Ja-Jager/griddles/docs/炸炉会议记录.md

# 会议记录

## 230109

时间：下午三点

参与方：陈希、丁鹏、杜淇宇

### 讨论内容

1. 早上大家的工作进度
    1. 阿杜：MAX6675 队列
    2. 阿鹏：主函数，队列邮箱，`protect`、seg、relay 已完成
    
2. Toaster 烘包机 driver 进度
    1. 完成：
       1. `protect`、seg、relay 之间
    2. 没完成：
       1. nvs 不需要用任务
       2. 按键
       3. 跨任务通信最花时间
          1. 

| **任务** | **负责人** | **完成了吗？** | 完成时间 |
| --- | --- | --- | --- |
| HC-SR04 | 阿鹏 | ✔ |  |
| MAX6675 | 阿杜 | ❌ |  |
| Nvs | 阿鹏 | ✔ |  |
| Protect | 阿杜 | ✔ |  |
| Relay | 阿鹏 | ✔ |  |
| SegmentDisplay | 阿鹏 | ✔ |  |
| Switch | 阿鹏 | ✔ |  |
| vl53l0x | 阿鹏 | ✔ |  |
| 主函数 | 阿鹏&阿杜  | ❌ |  |

2. ESP-IDF v5.0 升级 toaster
   1. 鹏没有问题
   2. 阿杜需要编译烘包机测试

3. 基于新增功能修改现有逻辑流程图
4. 炸炉引脚分配，如何减少引脚
   1. 用片选 IC

5. 炸炉增加 PWM 控温
6. 把 driver 里的代码移动到 component 中
7. 接下来的工作安排
   1. 阿杜：旋转编码器
   2. 阿鹏：继续主函数
      1. 炸炉：陈希提供阿鹏倒计时有什么函数
