Ja-Jager/griddles/docs/希与ROBIN的会议.md

# 希与ROBIN的会议

会议时间：2023.7.13

参会人员：希、ROBIN

会议目的：研究M3000（frymaster）的现有功能信息

希所能了解到的M3000的信息：

1. 油温（输入）

2. 蜂鸣器（输出）

3. 继电器（输出）

4. 升降机（输出）（暂未查出）

ROBIN的看法：

1. ROBIN认为蜂鸣器只能做到响来反映炸过一次菜单，但具体不知道是哪个菜单，什么时间点操作菜单。

2. 对于能耗，用电，现在只知道用的是哪个槽哪个继电器的吸合、断开，PWM，只能知道能耗是大是小，但还需知道它频率多少，用了多少电。假如发热管功率有衰减，只看继电器，能耗是看不出来的。需要有方法知道继电器的实时功率、功耗。

3. * 人生安全、财产安全：短路、着火，这些需要有故障提示
   
   * 食品安全：性能衰减，导致食物品质不行，性能方面的情况也需有故障提示
   
   需要当遇到故障时，需读取到一些故障代码，运行讯息。

4. 有没有可能远程修改菜单

5. ROBIN认为现在板子发出什么就把那个信号抓取，他发出的是哪一路的逻辑什么条件下触发 ，会出现什么报警，需破解其代码，破解它的控制。

6. 从烹饪的角度，要知道什么温度开启加热，什么温度停止加热，什么安全条件会出现报警，没达到什么条件会什么报警，是怎么进行温度补偿。

7. 这些输出量得研究，分难易先后去查找。

总结：

1. 暂时得到的这些油温、蜂鸣器、继电器、升降机不足以获取到炸炉的一些更细致的信息

2. 需了解电子板工作时，用了什么菜单、什么时候用的

3. 需了解电子板通过什么方式了解到发热管的实时功率、能耗

4. 需了解电子板在安全、品质方面是否有些故障提示

5. 需了解电子板是否有远程操作菜单、修改菜单的功能

6. ROBIN的建议：
   
   1. 需将板子上的输出量读取，发出接受什么信号就读什么信号
   
   2. 需破解其代码，了解其控制
   
   3. 对于以上这些，分难易先后去查找
