Ja-Jager/griddles/docs/技术文档(内部)/K型热电偶与热敏电阻的对比.md

# 热电偶与热敏电阻的测试对比

---

## 四探头

| 四探头绝缘 | 四探头位置 | 四探头的外部热传导 |四个探头的具体外观|
| --- | --- | --- |---|
|  |  |  ||

如图以上四图为了四个测温设备的互不干扰与公平，绝缘胶的层数相同，并用锡箔纸覆盖。

## 测试数据

### 测试操作

将温度处于室温的四个探头放入分3次投放入不同温度的液体中，观察其变化并记录，并记录在温度采集最稳定阶段的温度

### 温度数值

|测温设备| 80℃（沸水） | 114℃（油） | 168℃（油） |
|---| --- | ---- | ---- |
|**手持式温度计A**| 79.8℃ | 114.4℃ | 168℃ |
|**手持式温度计B**| 80.1℃ | 112.3℃ | 168℃ |
|**热敏电阻**| 80.54℃ | 111.84℃ | 158℃ |
|**热电偶**| 80.25℃ | 115℃ | 164℃ |

### 数据依据

| 80℃（沸水） | 114℃（油） | 160℃（油） |
| --- | --- | --- |
|  |  |  |

### 具体表格

| 80℃ |  |
| --- | --- |
| **114℃** |  |
| **168℃** |  |

## 结论

通过观察，热电偶的反应速度要快于热敏电阻的反应速度，且当温度平稳时，相较于热敏电阻，测出的温度更接近手持温度计的。故而热电偶优于热敏电阻。
