Ja-Jager/griddles/docs/技术文档(内部)/高端炸爐操作指南.md

# 高端炸爐操作指南

***更新时间：2023/9/11 18：00***

[TOC]

## 語言切換

1. 用戶通過左邊的橫欄【手动】、【计时】、【设置】，按下【设置】以**選擇**設置。

2. 滑動如下圖的**語言切換滾輪**。



### 使用流程

用戶通過自己的需求，可以用撥動**語言切換滾輪**來選擇心儀的語言。只要修改了，所有頁面的大多語言都會被修改。

## 手動操作

alt jpg

alt jpg

手動操作可以操作的位置有如上圖的4個位置。

1. 設定溫度滑條（量程：100℃ ~ 200℃，200℉ ~ 400℉）

2. 設定倒計時滑條（量程：15min，滑動的最小一格為10s）

3. 開始鍵

4. 旋鈕及旋鈕按鍵

### 烹飪流程

#### 用戶自定義操作

1. 用戶通過左邊的橫欄【手动】、【计时】、【设置】，按下【手动】以選擇**手動模式**。

2. 用戶通過自己的需求，可以用滑條或旋鈕**調整設定溫度**。（建議：滑條用於大幅度調整，旋鈕用於微小調整）。

3. 用戶通過自己的需求，可以用滑條**調整設定倒計時**。

4. 按下開始鍵或旋鈕，機器就會**開啓加熱**。

5. 按下開始鍵后，當溫度還**未到達設定溫度**時，【倒計時】下會顯示【預熱中】。

6. 當溫度達到設定溫度時，會出現一個頁面，提示投放食物。投放完食物后，按下屏幕上的【DONE】，**倒計時開啓**。

7. 當倒計時結束或客戶再次按下開始鍵或旋鈕按鍵，機器就會**結束倒計時，停止加熱**。

#### 无倒计时操作

1. 用戶通過自己的需求，可以用滑條或旋鈕調整設定溫度。（建議：滑條用於大幅度調整，旋鈕用於微小調整）。

2. 當溫度滑條拉至最左端，此時【設定倒計時】下會顯示【持續運行】。

3. 按下開始鍵或旋鈕，機器就會**開啓加熱**。

4. 按下開始鍵后，當溫度還**未到達設定溫度**時，【倒計時】下會顯示【預熱中】。

5. 當溫度**達到設定溫度**時，會出現一個頁面，提示投放食物。投放完食物后，按下屏幕上的【DONE】。

6. 客戶再次按下開始鍵，機器就會**停止加熱**。

## 自動操作

alt jpg



自動操作可以操作的位置有如上圖的3個位置。

1. 菜單滾輪

2. 開始鍵

3. 旋鈕及旋鈕按鍵

### 烹飪流程

1. 用戶通過左邊的橫欄【手动】、【计时】、【设置】，按下【自动】以選擇**自動模式**。

2.  用戶通過自己的需求，可以用滾輪或旋鈕**選擇**自己想要的**菜單**。

3. 按下開始鍵或旋鈕，機器就會**開啓加熱**。

4. 按下開始鍵后，當溫度還**未到達設定溫度**時，【倒計時】下會顯示【預熱中】。

5. 當溫度**達到設定溫度時**，會出現一個頁面，提示**投放食物**。投放完食物后，按下屏幕上的【DONE】，**倒計時開啓**。

6. 客戶再次按下開始鍵，機器就會**停止加熱**。

7. 當用戶用自動模式開啓加熱時，如果沒有切換界面，按下任何物理按鍵、開始鍵和滑動滾輪，就會彈出一個**屏保頁面**，類似與下圖。顯示的内容：倒計時、菜單名。

alt jpg

## 菜單操作

1. 用戶通過左邊的橫欄【手动】、【计时】、【设置】，按下【设置】以**選擇**設置。

2. 點擊如下圖的【menu】。



3. 點擊過後進入**用戶菜單**就會出現如下圖的針對菜單的3個操作：新增菜單、修改菜單、刪除菜單。



### 新增菜單

點擊**用戶菜單**的【Create Menu】,進入如下圖的**新增菜單頁面**。



新增菜單可以操作的位置有如上圖的4個位置。

1. 設定溫度滑條（量程：100℃ ~ 200℃，200℉ ~ 400℉）

2. 設定倒計時滑條（量程：15min，滑動的最小一格為10s）

3. 菜單列表

4. 新增菜單鍵

#### 使用流程

1. 用戶通過自己的需求，可以用滑條**調整設定溫度**。

2. 用戶通過自己的需求，可以用滑條**調整設定倒計時**。

3. 用戶通過自己的需求，可以用下拉式列表**選擇**心儀的**菜單名**。

4. 用戶確定完自己的選擇後，通過按下新增菜單鍵來**新增菜單**，新增的菜單出現將在**自動操作的滾輪選項**中。

### 編輯菜單

點擊**用戶菜單**的【Edit Menu】,進入如下圖的**編輯菜單頁面1**。

alt jpg

可以操作的位置有如上圖的2個位置。

1. 菜單列表（此列表中的選項都是自動操作頁面的滾輪選項）

2. 菜單名確定鍵

點擊**編輯菜單頁面1**的菜單確定鍵，進入如下圖的**編輯菜單**頁面2。

alt jpg

可以操作的位置有如上圖的3個位置。

1. 設定溫度滑條（量程：100℃ ~ 200℃，200℉ ~ 400℉）

2. 設定倒計時滑條（量程：15min，滑動的最小一格為10s）

3. 菜單修改確定鍵

#### 使用流程

1. 用戶通過自己的需求，可以用**菜單列表**選擇需要修改的**自動操作頁面的菜單選項**。

2. 按下菜單名確定鍵，進入**編輯菜單頁面2**。

3. 進入**編輯菜單頁面2**后，用戶通過自己的需求，可以用滑條**修改設定溫度**。

4. 用戶通過自己的需求，可以用滑條**修改設定倒計時**。

5. 用戶確定完自己的要修改的選擇後，通過按下**菜單修改確定鍵**來**修改菜單**，修改后的菜單會更新到**自動操作的滾輪選項**中。

### 刪除菜單

點擊**用戶菜單**的【Delete Menu】,進入如下圖的**刪除菜單頁面**。

alt jpg

可以操作的位置有如上圖的2個位置。

1. 菜單名滾輪（此列表中的選項都是自動操作頁面的滾輪選項）

2. 菜單刪除確定鍵

#### 使用流程

1. 用戶通過自己的需求，可以用**菜單名滾輪**選擇需要刪除的**自動操作頁面的菜單選項**。

2. 用戶確定完自己的要刪除的選擇後，通過按下**菜單刪除確定鍵**來**刪除菜單**，刪除后，菜單會更新到**自動操作的滾輪選項**中。

## 溫度單位切換

1. 用戶通過左邊的橫欄【手动】、【计时】、【设置】，按下【设置】以**選擇**設置。

2. 點擊如下圖的**溫度單位切換開關**。

alt jpg

### 使用流程

用戶通過自己的需求，可以用撥動**溫度單位切換開關**來選擇心儀的單位。只要修改了，手動操作、自動操作、新增菜單、修改菜單中的設定溫度和當前溫度的單位都會隨之變化。

## 演示模式

1. 用戶通過左邊的橫欄【手动】、【计时】、【设置】，按下【设置】以**選擇**設置。

2. 點擊如下圖的**演示模式開關**。



### 使用流程

當用戶對電子板不施加强電以供電時，可將**演示模式開關**打開，這樣就可以不受超溫保護、發熱管、泄油閥的影響用於演示。

**注意：當正常使用時，一定要關閉演示模式，否則超溫保護、發熱管、泄油閥將會失效。**

## 物理按鍵切換操作頁面



用戶可通過上圖的【模式】物理按鍵來切換操作頁面。

* 如果當前處於**自動操作頁面**，按下該鍵就會切換至**手動操作頁面**。

* 如果當前處於**手動操作頁面**，按下該鍵就會切換至**自動操作頁面**。

## 超溫保護、泄油、發熱管擡起

只要有出現**超溫保護、泄油、擡起發熱管**，機器將立刻**停止加熱，停止倒計時**。

**注意：正常烹炸食物時，一定要將演示模式關閉。**
