Ja-Jager/griddles/docs/技术文档(内部)/AVR版本/原高端炸炉引脚分配.md

# 原高端炸炉引脚分配

***更新于2023.2.1 10:30***

| 引脚名称 | 作用 |
| --- | --- |
| PE6/AOT2（LSW_A3） | 低电平使继电器通电，使得**左端子**的12、15脚相连，实现相关功能，信息反馈给LIN_B3引脚 |
| PE5/AOT3（LSW_A2） | 低电平使继电器通电，使得**左端子**的5、13脚相连，实现相关功能，信息反馈给LIN_B5引脚 |
|PE4/AOT4（LSW_A1）|低电平使继电器通电，使得**左端子**的10、12脚相连，实现相关功能，信息反馈给LIN_B3引脚|
|PE3/AOT5（ASW_1）|低电平使继电器通电，使得ACOUTA与交流220V相连，此功能现在空置，ACOUTA功能未知|
|PE2/AOT6（ASW_2）|低电平使继电器通电，使得ACOUTB与交流220V相连，此功能现在空置，ACOUTB功能未知|
|PG5/AOT8|使能蜂鸣器|
|PH0/LIN_B1|**左端子**的2、7脚相连，信息反馈给LIN_B1|
|PH1/LIN_B2|**左端子**的6、11脚相连，信息反馈给LIN_B2|
|PH2/LIN_B3|参考上述AOT2、4|
|PH3/LIN_B4|**左端子**的4、8脚相连，信息反馈给LIN_B4|
|PH4/LIN_B5|参考上述AOT3|
|PJ6/LROUT5(RSW_A3)|低电平使继电器通电，使得**右端子**的12、15脚相连，实现相关功能，信息反馈给RIN_B3引脚|
|PJ5/LROUT6(RSW_A2)|低电平使继电器通电，使得**右端子**的5、13脚相连，实现相关功能，信息反馈给RIN_B5引脚|
|PJ4/LROUT7(RSW_A1)|低电平使继电器通电，使得**右端子**的10、12脚相连，实现相关功能，信息反馈给RIN_B3引脚|
|PJ3/LROUT8(DATA_OUT)|备用接口，连接JP1，此功能空置|
|PC6/DATA_INA|备用接口，连接JP1，JP1将信息反馈给DATA_INA，此功能空置|
|PC5/DATA_INB|备用接口，连接JP1，JP1将信息反馈给DATA_INB，此功能空置|
|PC4/RIN_B1|**右端子**的2、7脚相连，信息反馈给RIN_B1|
|PC3/RIN_B2|**右端子**的6、11脚相连，信息反馈给RIN_B2|
|PC2/RIN_B3|参考上述LROUT5、7|
|PC1/RIN_B4|**右端子**的4、8脚相连，信息反馈给RIN_B2|
|PC0/RIN_B5|参考上述LROUT6|
|PL3/X_SW_1|连接显示按键接口|
|PL2/X_SW_2|连接显示按键接口|
|PL1/X_SW_3|连接显示按键接口|
|PL0/X_SW_4|连接显示按键接口|
|PD6/X_DIO|连接显示按键接口|
|PD5/X_CLK|连接显示按键接口|
|PD4/X_ASTB|连接显示按键接口|
|PD1/X_BSTB|连接显示按键接口|
|PD0/X_CSTB|连接显示按键接口|
|PL7/X_DSTB|连接显示按键接口|
|PL6/X_ESTB|连接显示按键接口|
|PL5/X_FSTB|连接显示按键接口|
|PL4/X_GSTB|连接显示按键接口|
|PA3/IN1A|备用接口，连接U13，此功能空置|
|PA4/IN1B|备用接口，连接U13，此功能空置|
|PA5/IN2A|备用接口，连接U12，此功能空置|
|PA6/IN2B|备用接口，连接U12，此功能空置|
|PJ2/485_EN|备用接口，RS485通讯，此功能空置|
|PJ0/485_RXD|备用接口，RS485通讯，此功能空置|
|PJ1/485_TXD|备用接口，RS485通讯，此功能空置|
|PG1/EP_DIO|用于EEPROM|
|PG0/EP_CLK|用于EEPROM|
|PD7/EP_STB|用于EEPROM|
|PH5/R_CLK|用于断电后提供时钟，可能用于显示实时时间|
|PH6/R_DIO|用于断电后提供时钟，可能用于显示实时时间|
|PB0/R_STB|用于断电后提供时钟，可能用于显示实时时间|
|PB1/SPI_SCK|用于烧写程序|
|PB2/SPI_MOSI|用于烧写程序|
|PB3/SPI_MISO|用于烧写程序|
|RESET/RESET|用于烧写程序时的复位，也可用于微处理器的复位|
|PK6/L_TER|用于左温度探头|
|PK7/R_TER|用于右温度探头|
|PK5/ADC_NTC|用于接收探头的反馈信息|
|PE0/RXD0|用于备用收发，此功能空置|
|PE1/TXD0|用于备用收发，此功能空置|
|PD2/RXD1|用于蓝牙、wifi功能收发|
|PD3/TXD1|用于蓝牙、wifi功能收发|
|AREF/AREF|基准电压输入引脚|

总共60个引脚，空置14个，实用46个。
