Ja-Jager/griddles/docs/技术文档(内部)/V2.2.0/关于稳压器件AMS1117过热的处理.md

# 关于稳压器件AMS1117过热的处理

***2023/7/3 16:00***

$$
P_{\text{Dissipated}} = (V_{\text{in}} - V_{\text{out}}) \times I
$$

$$
T_{\text{AboveAmbient}} = P_{\text{Dissipated}} \times 55
$$

$$
T_{\text{Final}} = T_{\text{Dissipated}} + T_{\text{Ambient}}
$$

$$
P_{\text{Dissipated}} = (5.00 - 3.281) \times I = 1.719I
$$

$$
T_{\text{AboveAmbientLOW}} = 1.719I\times 55=94.545I
$$

$$
T_{\text{AboveAmbientHI}} = 1.719I\times 80=137.52I
$$

$$
T_{\text{Final}} = T_{\text{DissipatedHI}} + T_{\text{Ambient}}
$$

$$
80=137.52I(LOW)+28
$$

$$
I(LOW)=0.378A
$$

$$
80=94.545I(HI)+28
$$

$$
I(HI)=0.550A
$$

[Microsoft Word - DS1117 (advanced-monolithic.com)](http://www.advanced-monolithic.com/pdf/ds1117.pdf)

参考第三页。

最终决定：将AMS1117封装从SOT-223换成TO-252，胶不覆盖器件表面，引脚可覆盖。
