Ja-Jager/griddles/docs/技术文档(内部)/V2.0.0/除了7寸屏外剩余的9个引脚分配.md

# 除了7寸屏外剩余的9个引脚分配

## 单独

| 功能 | 引脚占用数 |
| --- | --- |
| *** 温度探头（ADC）*** | 1 |
| ***继电器K9（ADC）*** | 1 |
|***4个按键（ADC）***|1|
| ***旋钮A*** | 1 |
| ***旋钮B*** | 1 |

## 多输出移位寄存器（74HC595）

| 功能 | 引脚总占用数 |
| --- | --- |
| 蜂鸣器 | 3 |

## 多输入移位寄存器（74HC165）

| 功能 | 引脚总占用数 |
| --- | --- |
| ***光耦P5*** | 2 |
| ***光耦P6*** | |
|***光耦P7***||
