Ja-Jager/griddles/docs/技术文档(内部)/流程图/微信图片_20230209092502.jpg

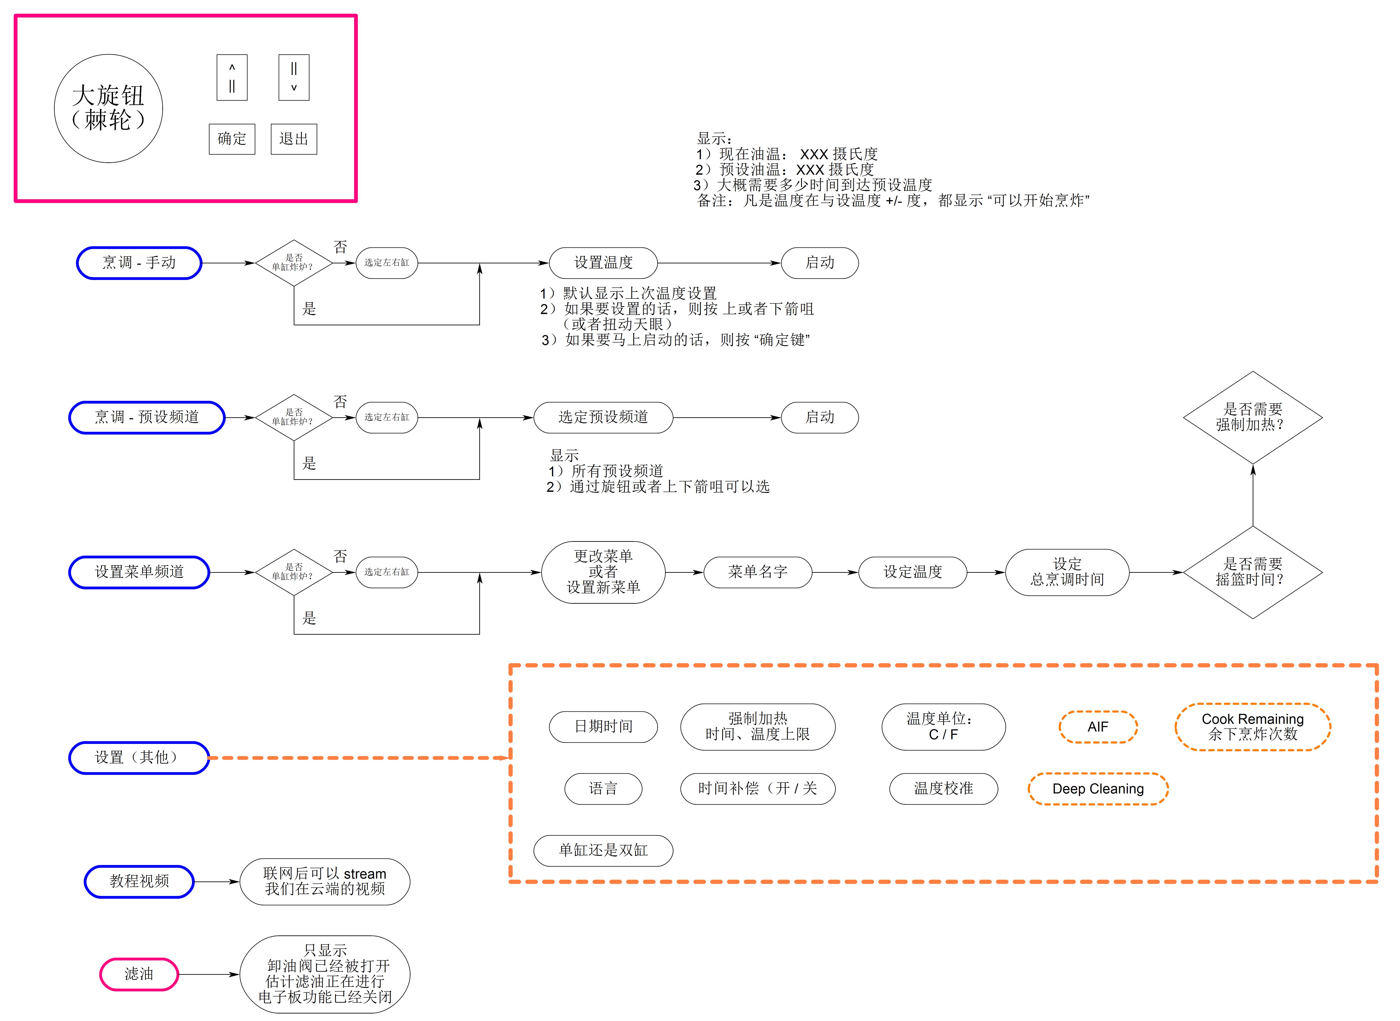
docs/技术文档(内部)/流程图/微信图片_20230209092502.jpg
