Ja-Jager/griddles/docs/技术文档(内部)/流程图/自定义菜单流程图.jpg

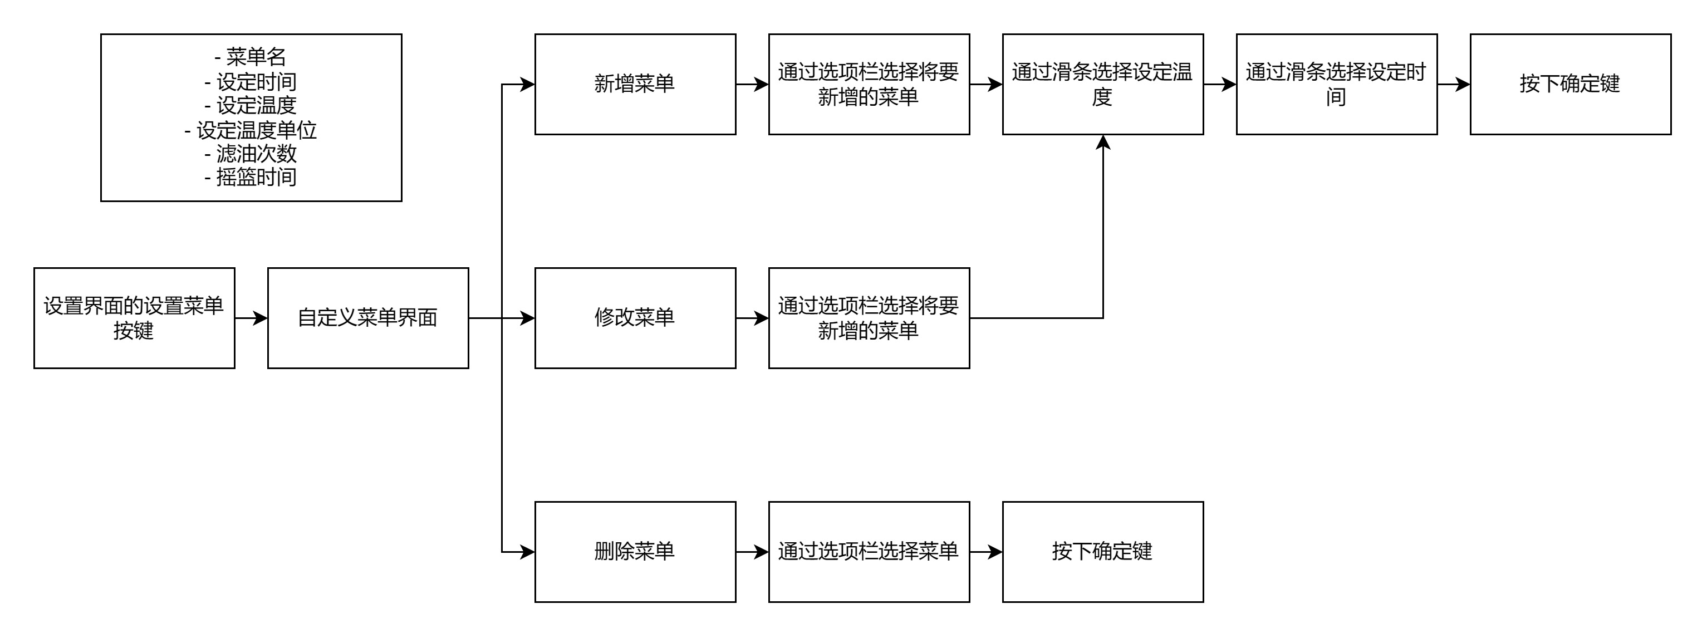
docs/技术文档(内部)/流程图/自定义菜单流程图.jpg
