Ja-Jager/griddles/components/ws_7inch/include/bsp/ws_7inch.h

/*
 * SPDX-FileCopyrightText: 2022 Espressif Systems (Shanghai) CO LTD
 *
 * SPDX-License-Identifier: CC0-1.0
 */

#pragma once

#include "sdkconfig.h"
#include "driver/gpio.h"
#include "driver/i2c.h"
#include "lvgl.h"

/**************************************************************************************************
 *  ESP-BOX pinout
 **************************************************************************************************/
// /* V2.0.0 */
// /* I2C */
// #define BSP_I2C_SCL (GPIO_NUM_21)
// #define BSP_I2C_SDA (GPIO_NUM_47)

// /* Display */
// #define BSP_LCD_WIDTH (16)
// #define BSP_LCD_DB0 (GPIO_NUM_12)
// #define BSP_LCD_DB1 (GPIO_NUM_13)
// #define BSP_LCD_DB2 (GPIO_NUM_10)
// #define BSP_LCD_DB3 (GPIO_NUM_11)
// #define BSP_LCD_DB4 (GPIO_NUM_46)
// #define BSP_LCD_DB5 (GPIO_NUM_9)
// #define BSP_LCD_DB6 (GPIO_NUM_8)
// #define BSP_LCD_DB7 (GPIO_NUM_3)
// #define BSP_LCD_DB8 (GPIO_NUM_17)
// #define BSP_LCD_DB9 (GPIO_NUM_18)
// #define BSP_LCD_DB10 (GPIO_NUM_41)
// #define BSP_LCD_DB11 (GPIO_NUM_42)
// #define BSP_LCD_DB12 (GPIO_NUM_39)
// #define BSP_LCD_DB13 (GPIO_NUM_40)
// #define BSP_LCD_DB14 (GPIO_NUM_37)
// #define BSP_LCD_DB15 (GPIO_NUM_38)
// #define BSP_LCD_CS (GPIO_NUM_NC)
// #define BSP_LCD_DC (GPIO_NUM_4)
// #define BSP_LCD_WR (GPIO_NUM_36)
// #define BSP_LCD_RD (GPIO_NUM_NC)
// #define BSP_LCD_RST (GPIO_NUM_35)
// #define BSP_LCD_WAIT (GPIO_NUM_48)
// #define BSP_LCD_BL (GPIO_NUM_NC)
// #define BSP_LCD_TP_INT (GPIO_NUM_45)

// /* V2.1.0 */
// /* I2C */
// #define BSP_I2C_SCL (GPIO_NUM_13)
// #define BSP_I2C_SDA (GPIO_NUM_12)

// /* Display */
// #define BSP_LCD_WIDTH (16)
// #define BSP_LCD_DB0 (GPIO_NUM_47)
// #define BSP_LCD_DB1 (GPIO_NUM_21)
// #define BSP_LCD_DB2 (GPIO_NUM_48)
// #define BSP_LCD_DB3 (GPIO_NUM_45)
// #define BSP_LCD_DB4 (GPIO_NUM_35)
// #define BSP_LCD_DB5 (GPIO_NUM_36)
// #define BSP_LCD_DB6 (GPIO_NUM_37)
// #define BSP_LCD_DB7 (GPIO_NUM_38)
// #define BSP_LCD_DB8 (GPIO_NUM_39)
// #define BSP_LCD_DB9 (GPIO_NUM_40)
// #define BSP_LCD_DB10 (GPIO_NUM_41)
// #define BSP_LCD_DB11 (GPIO_NUM_42)
// #define BSP_LCD_DB12 (GPIO_NUM_17)
// #define BSP_LCD_DB13 (GPIO_NUM_18)
// #define BSP_LCD_DB14 (GPIO_NUM_8)
// #define BSP_LCD_DB15 (GPIO_NUM_3)
// #define BSP_LCD_CS (GPIO_NUM_NC)
// #define BSP_LCD_DC (GPIO_NUM_2)
// #define BSP_LCD_WR (GPIO_NUM_46)
// #define BSP_LCD_RD (GPIO_NUM_NC)
// #define BSP_LCD_RST (GPIO_NUM_9)
// #define BSP_LCD_WAIT (GPIO_NUM_11)
// #define BSP_LCD_BL (GPIO_NUM_NC)
// #define BSP_LCD_TP_INT (GPIO_NUM_10)

/* V2.1.1 */
/* I2C */
// #define BSP_I2C_SCL (GPIO_NUM_12)
// #define BSP_I2C_SDA (GPIO_NUM_13)

// /* Display */
// #define BSP_LCD_WIDTH (16)
// #define BSP_LCD_DB0 (GPIO_NUM_42)
// #define BSP_LCD_DB1 (GPIO_NUM_41)
// #define BSP_LCD_DB2 (GPIO_NUM_40)
// #define BSP_LCD_DB3 (GPIO_NUM_39)
// #define BSP_LCD_DB4 (GPIO_NUM_38)
// #define BSP_LCD_DB5 (GPIO_NUM_37)
// #define BSP_LCD_DB6 (GPIO_NUM_36)
// #define BSP_LCD_DB7 (GPIO_NUM_35)
// #define BSP_LCD_DB8 (GPIO_NUM_45)
// #define BSP_LCD_DB9 (GPIO_NUM_48)
// #define BSP_LCD_DB10 (GPIO_NUM_47)
// #define BSP_LCD_DB11 (GPIO_NUM_21)
// #define BSP_LCD_DB12 (GPIO_NUM_3)
// #define BSP_LCD_DB13 (GPIO_NUM_8)
// #define BSP_LCD_DB14 (GPIO_NUM_18)
// #define BSP_LCD_DB15 (GPIO_NUM_17)
// #define BSP_LCD_CS (GPIO_NUM_NC)
// #define BSP_LCD_DC (GPIO_NUM_2)
// #define BSP_LCD_WR (GPIO_NUM_46)
// #define BSP_LCD_RD (GPIO_NUM_NC)
// #define BSP_LCD_RST (GPIO_NUM_9)
// #define BSP_LCD_WAIT (GPIO_NUM_11)
// #define BSP_LCD_BL (GPIO_NUM_NC)
// #define BSP_LCD_TP_INT (GPIO_NUM_10)

/* V2.2.0 */
/* I2C */
#define BSP_I2C_SCL (GPIO_NUM_12)
#define BSP_I2C_SDA (GPIO_NUM_13) 

/* Display */
#define BSP_LCD_WIDTH (16)
#define BSP_LCD_DB0 (GPIO_NUM_42)
#define BSP_LCD_DB1 (GPIO_NUM_41)
#define BSP_LCD_DB2 (GPIO_NUM_40)
#define BSP_LCD_DB3 (GPIO_NUM_39)
#define BSP_LCD_DB4 (GPIO_NUM_38)
#define BSP_LCD_DB5 (GPIO_NUM_37)
#define BSP_LCD_DB6 (GPIO_NUM_36)
#define BSP_LCD_DB7 (GPIO_NUM_35)
#define BSP_LCD_DB8 (GPIO_NUM_45)
#define BSP_LCD_DB9 (GPIO_NUM_48)
#define BSP_LCD_DB10 (GPIO_NUM_47)
#define BSP_LCD_DB11 (GPIO_NUM_21)
#define BSP_LCD_DB12 (GPIO_NUM_3)
#define BSP_LCD_DB13 (GPIO_NUM_8)
#define BSP_LCD_DB14 (GPIO_NUM_18)
#define BSP_LCD_DB15 (GPIO_NUM_17)
#define BSP_LCD_CS (GPIO_NUM_NC)
#define BSP_LCD_DC (GPIO_NUM_2)
#define BSP_LCD_WR (GPIO_NUM_46)
#define BSP_LCD_RD (GPIO_NUM_NC)
#define BSP_LCD_RST (GPIO_NUM_9)
#define BSP_LCD_WAIT (GPIO_NUM_11)
#define BSP_LCD_BL (GPIO_NUM_NC)
#define BSP_LCD_TP_INT (GPIO_NUM_10)

// /* general band */
// /* I2C */
// #define BSP_I2C_SCL (GPIO_NUM_17)
// #define BSP_I2C_SDA (GPIO_NUM_18)

// /* Display */
// #define BSP_LCD_WIDTH (16)
// #define BSP_LCD_DB0 (GPIO_NUM_42)
// #define BSP_LCD_DB1 (GPIO_NUM_41)
// #define BSP_LCD_DB2 (GPIO_NUM_40)
// #define BSP_LCD_DB3 (GPIO_NUM_39)
// #define BSP_LCD_DB4 (GPIO_NUM_38)
// #define BSP_LCD_DB5 (GPIO_NUM_37)
// #define BSP_LCD_DB6 (GPIO_NUM_36)
// #define BSP_LCD_DB7 (GPIO_NUM_35)
// #define BSP_LCD_DB8 (GPIO_NUM_45)
// #define BSP_LCD_DB9 (GPIO_NUM_48)
// #define BSP_LCD_DB10 (GPIO_NUM_47)
// #define BSP_LCD_DB11 (GPIO_NUM_21)
// #define BSP_LCD_DB12 (GPIO_NUM_14)
// #define BSP_LCD_DB13 (GPIO_NUM_13)
// #define BSP_LCD_DB14 (GPIO_NUM_12)
// #define BSP_LCD_DB15 (GPIO_NUM_11)
// #define BSP_LCD_CS (GPIO_NUM_NC)
// #define BSP_LCD_DC (GPIO_NUM_10)
// #define BSP_LCD_WR (GPIO_NUM_9)
// #define BSP_LCD_RD (GPIO_NUM_NC)
// #define BSP_LCD_RST (GPIO_NUM_46)
// #define BSP_LCD_WAIT (GPIO_NUM_8)
// #define BSP_LCD_BL (GPIO_NUM_NC)
// #define BSP_LCD_TP_INT (GPIO_NUM_3)

#ifdef __cplusplus
extern "C"
{
#endif

/**************************************************************************************************
 *
 * I2C interface
 *
 * There are multiple devices connected to I2C peripheral:)
 *  - LCD Touch controller
 *
 * After initialization of I2C, use BSP_I2C_NUM macro when creating I2C devices drivers ie.:
 * \code{.c}
 * es8311_handle_t es8311_dev = es8311_create(BSP_I2C_NUM, ES8311_ADDRRES_0);
 * \endcode
 **************************************************************************************************/
#define BSP_I2C_NUM 1
#define BSP_I2C_CLK_SPEED_HZ 400000

    /**
     * @brief Init I2C driver
     *
     */
    esp_err_t bsp_i2c_init(void);

    /**
     * @brief Deinit I2C driver and free its resources
     *
     */
    esp_err_t bsp_i2c_deinit(void);

/**************************************************************************************************
 *
 * LCD interface
 *
 * This display has 7inch and RA8875 display controller.
 * It features 16-bit colors, 800x480 resolution and capacitive touch controller GT911.
 *
 * LVGL is used as graphics library. LVGL is NOT thread safe, therefore the user must take LVGL mutex
 * by calling bsp_display_lock() before calling and LVGL API (lv_...) and then give the mutex with
 * bsp_display_unlock().
 *
 * Display's backlight must be enabled explicitly by calling bsp_display_backlight_on()
 **************************************************************************************************/
#define BSP_LCD_H_RES (800)
#define BSP_LCD_V_RES (480)
#define BSP_LCD_PIXEL_CLOCK_HZ (20 * 1000 * 1000)

    /**
     * @brief Initialize display
     *
     * This function initializes SPI, display controller and starts LVGL handling task.
     * LCD backlight must be enabled separately by calling bsp_display_brightness_set()
     *
     * @return Pointer to LVGL display or NULL when error occured
     */
    lv_disp_t *bsp_display_start(void);

    /**
     * @brief Take LVGL mutex
     *
     * @param timeout_ms Timeout in [ms]. 0 will block indefinitely.
     * @return true  Mutex was taken
     * @return false Mutex was NOT taken
     */
    bool bsp_display_lock(uint32_t timeout_ms);

    /**
     * @brief Give LVGL mutex
     *
     */
    void bsp_display_unlock(void);

    /**
     * @brief Set display's brightness
     *
     * Brightness is controlled with PWM signal to a pin controling backlight.
     *
     * @param[in] brightness_percent Brightness in [%]
     * @return
     *      - ESP_OK                On success
     *      - ESP_ERR_INVALID_ARG   Parameter error
     */
    esp_err_t bsp_display_brightness_set(int brightness_percent);

    /**
     * @brief Turn on display backlight
     *
     * Display must be already initialized by calling bsp_display_start()
     *
     * @return
     *      - ESP_OK                On success
     *      - ESP_ERR_INVALID_ARG   Parameter error
     */
    esp_err_t bsp_display_backlight_on(void);

    /**
     * @brief Turn off display backlight
     *
     * Display must be already initialized by calling bsp_display_start()
     *
     * @return
     *      - ESP_OK                On success
     *      - ESP_ERR_INVALID_ARG   Parameter error
     */
    esp_err_t bsp_display_backlight_off(void);

    /**
     * @brief Rotate screen
     *
     * Display must be already initialized by calling bsp_display_start()
     *
     * @param[in] disp Pointer to LVGL display
     * @param[in] rotation Angle of the display rotation
     */
    void bsp_display_rotate(lv_disp_t *disp, lv_disp_rot_t rotation);

#ifdef __cplusplus
}
#endif
